Elektrofix-OL/IR-Lesekopf-fuer-SmartMeter/Eagle/D0-Shield.sch

## EAGLE design Eagle/D0-Shield.sch (2021-12-25)

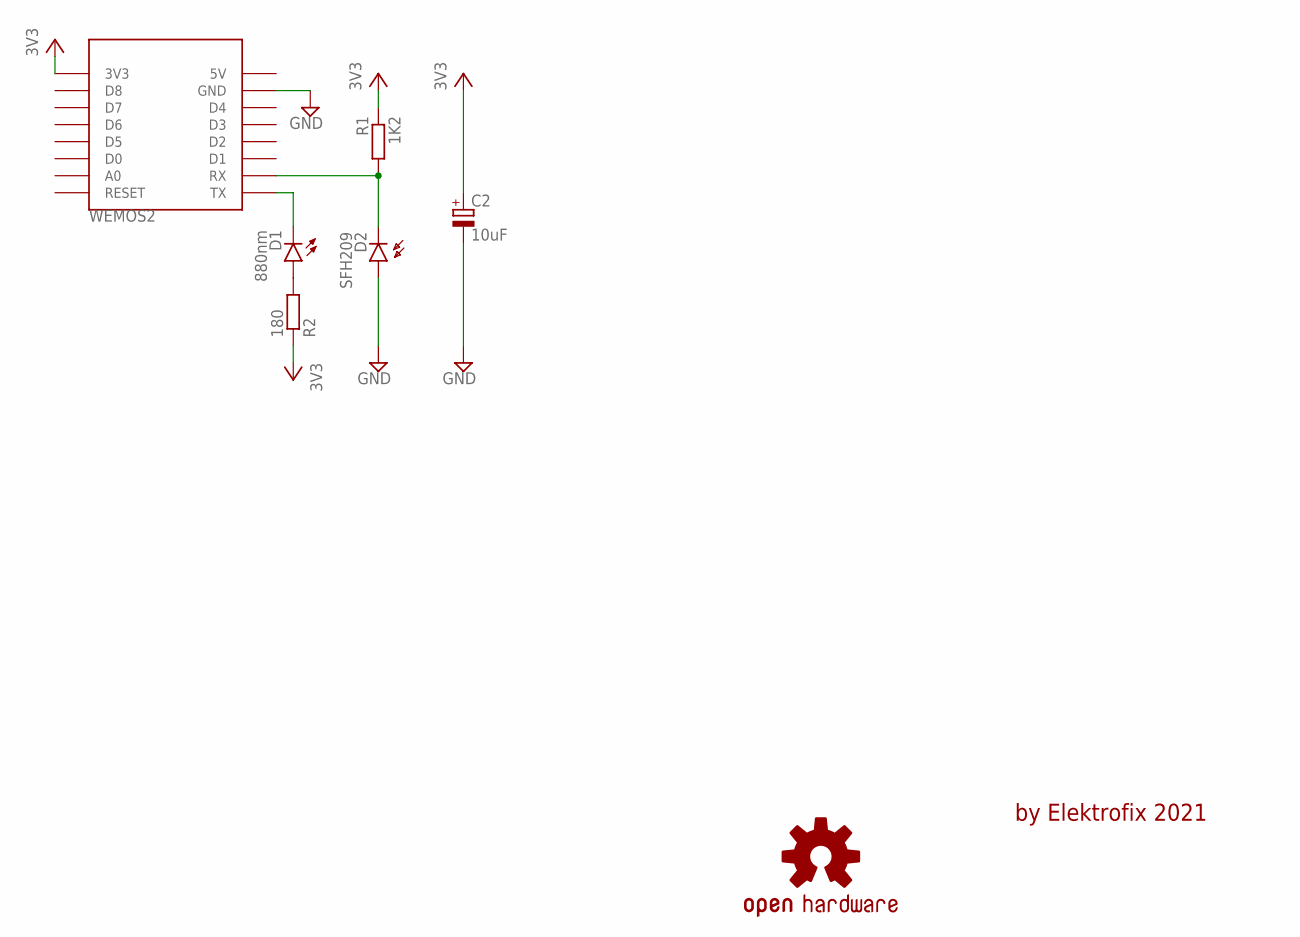
[picture p8: schematic D0-Shield.sch]

Parts:
C2: 10uF; E3,5-8
D1: 880nm; SFH482
D2: SFH209; SFH205
LOGO1: OSHW-LOGOL; OSHW-LOGO-L
R1: 1K2; 0207/12
R2: 180; 0207/12
WEMOS2: WEMOS-D1-MINI

Connections:
3V3: R1.1, R2.1, WEMOS2.3V3
GND: C2.-, D2.A, WEMOS2.GND
unnamed: D1.A, R2.2
unnamed: D1.K (C), WEMOS2.TX
unnamed: D2.K (C), R1.2, WEMOS2.RX
VCC: C2.+

Notes on the sheet:
by Elektrofix 2021
